cnlohr/beanboy/firmware/assets.h

#ifndef _ASSETS_H
#define _ASSETS_H

#include <stdint.h>

typedef struct {
	int16_t w;
	int16_t h;
	const uint32_t data[];
} bsprite;

const bsprite closed_box   __attribute__((section(".rodata"))) = {
	.w = 8,
	.h = 60,
	.data = {
		0xffffffff, 0xffffffff, 0xffffffff, 0xffffffff, 0xffffffff, 0xffffffff, 0xffffffff, 0x3fff3fff, 
		0x0001ffff, 0x0000ffff, 0x0000ffff, 0x0200ffff, 0x0010ffff, 0x0000ffff, 0x0000ffff, 0x20003fff, 
		0x0001ffff, 0x0000ffff, 0x0000ffff, 0x0200ffff, 0x0010ffff, 0x0000ffff, 0x0000ffff, 0x20003fff, 
		0x0001ffff, 0x0000ffff, 0x0000ffff, 0x0200ffff, 0x0010ffff, 0x0000ffff, 0x0000ffff, 0x20003fff, 
		0x0001ffff, 0x0000ffff, 0x0000ffff, 0x0200ffff, 0x0010ffff, 0x0000ffff, 0x0000ffff, 0x20003fff, 
		0x0001ffff, 0x0000ffff, 0x0000ffff, 0x0200ffff, 0x0010ffff, 0x0000ffff, 0x0000ffff, 0x20003fff, 
		0x0001ffff, 0x0000ffff, 0x0000ffff, 0x0200ffff, 0x0010ffff, 0x0000ffff, 0x0000ffff, 0x20003fff, 
		0x0001ffff, 0x0000ffff, 0x0000ffff, 0x0200ffff, 0x0010ffff, 0x0000ffff, 0x0000ffff, 0x20003fff, 
		0x0001ffff, 0x0000ffff, 0x0000ffff, 0x0200ffff, 0x0010ffff, 0x0000ffff, 0x0000ffff, 0x20003fff, 
		0x0001ffff, 0x0000ffff, 0x00fcffff, 0x0200ffff, 0x0010ffff, 0x0fc0ffff, 0x0000ffff, 0x20003fff, 
		0x0001ffff, 0x0000ffff, 0x1f03ffff, 0x0200ffff, 0x0010ffff, 0x303effff, 0x0000ffff, 0x20003fff, 
		0x0001ffff, 0xc000ffff, 0x6000ffff, 0x0200ffff, 0x8010ffff, 0xc001ffff, 0x0000ffff, 0x20003fff, 
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
		0xfff0fff0, 0xffffffff, 0x1fff1fff, 0x00000000, 0xffe0ffe0, 0xffffffff, 0x0fff0fff, 0x00000000, 
		0xff40ffc0, 0xffffffff, 0x07ff07ff, 0x00000000, 0xff80ffc0, 0xffffffff, 0x03ff07ff, 0x00000000, 
		0xf780ffc0, 0xffffffff, 0x03ff07ff, 0x00000000, 0xfb80ffc0, 0xffffffff, 0x03ef07ff, 0x00000000, 
		0xfc80ffc0, 0xffffffff, 0x031f07ff, 0x00000000, 0xf000f0c0, 0xffffffff, 0x001f071f, 0x00000000, 
		0xc000c000, 0xffffffff, 0x00070007, 0x00000000, 0x00000000, 0xfbffffff, 0x00010001, 0x00000000, 
		0x00000000, 0x3bd83ff8, 0x00000000, 0x00000000, 0x00000000, 0x018003c0, 0x00000000, 0x00000000, 
		0x00000000, 0x01000380, 0x00000000, 0x00000000, 0x00000000, 0x00000100, 0x00000000, 0x00000000, 
	}
};

#endif
